AllenNeuralDynamics/harp.device.cuttlefish-fip/firmware/tests/pulsetrain/main.cpp

#include <pico/stdlib.h>
#include <cstdio>
#include <cstdint>
#include <iterator>
#include <pulse_train_task.h>

inline constexpr uint32_t LED_PIN = 25;

// Create a pulse task w/static mem allocation.
pulse_event_t pulse_events[] = {{1, 0}, {0, 100'000}, {1, 200'000}, {0, 300'000}};
pulse_event_t* pulse_event_ptrs[] = {&pulse_events[0], &pulse_events[1], &pulse_events[2], &pulse_events[3]};

PulseTrainTask pulse_task(pulse_event_ptrs, std::size(pulse_events), 1'000'000,
                          1 << LED_PIN);



int main()
{
    stdio_usb_init();
    stdio_set_translate_crlf(&stdio_usb, false); // Don't replace outgoing chars.
    while (!stdio_usb_connected()){} // Block until connection to serial port.
    printf("Hello, world!\r\n");

    pulse_task.start();
    while(true)
        pulse_task.spin();
}
